laneboysrc/rc-headless-transmitter/transmitter/firmware/configuration/config.h

#pragma once

#include <channels.h>
#include <inputs.h>
#include <limits.h>
#include <mixer.h>
#include <protocol_hk310.h>


#define CONFIG_VERSION 1

typedef enum {
    RF_PROTOCOL_HK310,
    RF_PROTOCOL_LANEBOYSRC4CH,
    RF_PROTOCOL_LANEBOYSRC8CH
} rf_protocol_type_t;

typedef struct {
    uint8_t uuid[8];
    char name[16];
    uint32_t last_changed;
    uint32_t tag;               // For use by the configurator internally
    hardware_input_t hardware_inputs[MAX_TRANSMITTER_INPUTS];
    logical_input_t logical_inputs[MAX_LOGICAL_INPUTS];
    int32_t trim_range;
    int32_t trim_step_size;
    uint32_t bind_timeout_ms;
    uint32_t double_click_timeout_ms;
    uint16_t passphrase;
    uint8_t led_pwm_percent;
    uint8_t meter_pwm_percent;
} tx_t;

typedef struct {
    uint8_t uuid[8];
    char name[16];
    uint32_t last_changed;
    uint32_t tag;               // For use by the configurator internally
    mixer_unit_t mixer_units[MAX_MIXER_UNITS];
    limits_t limits[NUMBER_OF_RF_CHANNELS];
    rf_protocol_type_t rf_protocol_type;
    union {
        protocol_hk310_t protocol_hk310;
    } rf;
}  model_t;

typedef struct {
    uint32_t version;
    tx_t tx;
    model_t model;
} config_t;


extern config_t config;
extern const config_t config_flash;

void CONFIG_init(void);
void CONFIG_load(void);
void CONFIG_save(void);
void CONFIG_background_flash_write(void);
void CONFIG_dump_javascript_information(void);
