laneboysrc/rc-headless-transmitter/configurator/usb-dongle/firmware/system/systick.h

#pragma once

#include <stdint.h>


typedef void (* systick_callback)(void);

extern volatile uint32_t milliseconds;

void SYSTICK_init(void);
void SYSTICK_set_callback(systick_callback cb, uint32_t duration_ms);
void SYSTICK_clear_callback(systick_callback cb);
