laneboysrc/rc-headless-transmitter/transmitter/firmware/system/persistent_storage.h

#pragma once

void PERSISTENT_STORAGE_init(void);
void PERSISTENT_STORAGE_background_flash_write(void);
void PERSISTENT_STORAGE_save_config(void);
void PERSISTENT_STORAGE_save_hardware_input_values(void);
